H0nz4k/485_elatec/docs/mechanical_extract/docrev10_page_06.png

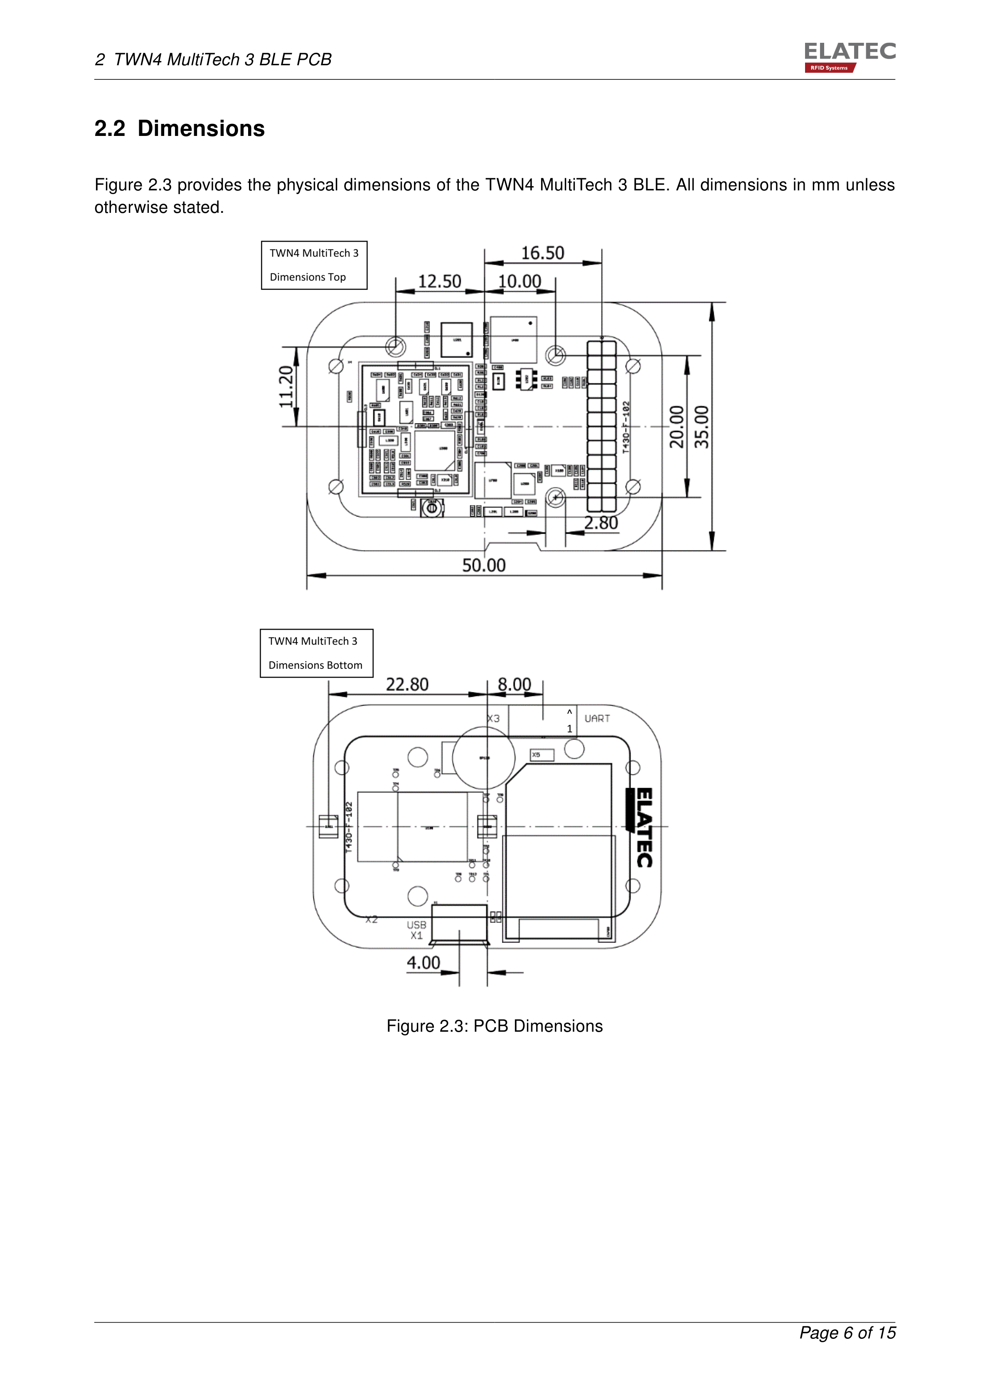
docs/mechanical_extract/docrev10_page_06.png
