H0nz4k/485_elatec/docs/mechanical_extract/right_x2_area_top_crop.png

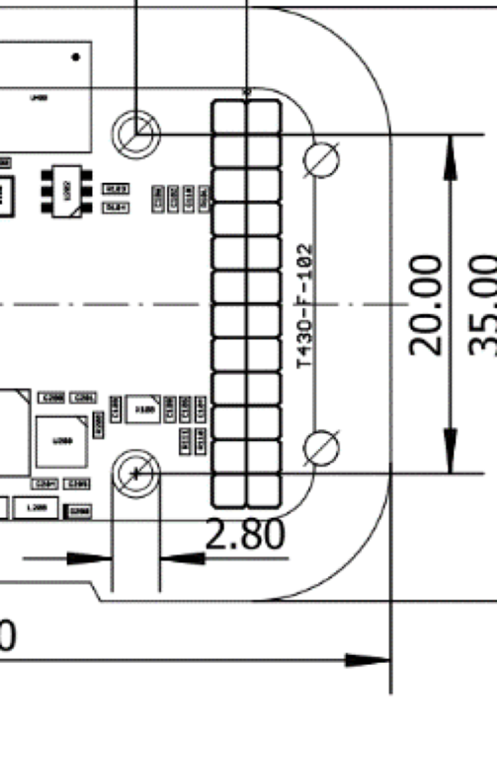
docs/mechanical_extract/right_x2_area_top_crop.png
