H0nz4k/485_elatec/manufacturing/rev_b/README_JLCPCB.md

# Rev B JLCPCB Manufacturing Package

Status: NOT READY TO ORDER.

## Current Contents

- `bom/rev_b_kicad_bom.csv` - BOM exported from the Rev B schematic
- `assembly_notes.md`
- `known_risks.md`
- `prototype_test_plan.md`

## Missing Before Order

- Validated PCB layout
- Gerbers
- Drill files
- Pick and Place / CPL
- Final JLCPCB/LCSC part mapping
- Final assembly decision for hand-soldered parts
- Gerber viewer review
- DRC report

## Ordering Decision

Do not submit this folder to JLCPCB yet. It is a scaffold for the manufacturing package, not a completed package.
