H0nz4k/485_elatec/manufacturing/rev_c/assembly_notes.md

# Rev C Assembly Notes

Status: Preview only.

Do not assemble from this package until routing, DRC and visual review are complete.

## Current Use

This folder verifies that KiCad can produce the expected manufacturing file types for Rev C.

## Not Yet Validated

- Pick and place orientation.
- Connector orientation.
- TWN4 X2 mechanical alignment.
- Soldermask/silkscreen clearance.
- Hand-assembly list.
- LCSC availability.
