H0nz4k/485_elatec/manufacturing/rev_c/manufacturing_checklist.md

# Rev C Manufacturing Checklist

## Completed

- [x] Rev C PCB file exists.
- [x] All schematic components are represented as PCB footprints.
- [x] DRC command runs.
- [x] Gerbers export.
- [x] Drill file exports.
- [x] CPL exports.
- [x] BOM exists.
- [x] PDF preview exports.
- [x] Geometry DRC cleanup pass completed.
- [x] Specctra DSN exported from KiCad GUI.
- [x] Freerouting completed.
- [x] SES imported back into KiCad.
- [x] Routed PCB saved.
- [x] KiCad DRC after Freerouting import: 0 violations.
- [x] KiCad unconnected pads after Freerouting import: 0.

## Blocking

- [x] PCB routed.
- [x] Connectivity/ratsnest clean.
- [ ] Schematic parity checked.
- [ ] Gerbers visually reviewed.
- [ ] CPL manually reviewed.
- [ ] TWN4 X2 mechanics verified.
- [ ] Lock current trace widths verified.
- [ ] Buck layout reviewed against datasheet.
- [ ] JLCPCB/LCSC part mapping completed.

## Decision

Do not order Rev C yet.
